tchen01/fadecandy/doc/images/controller-internals-diagram.png

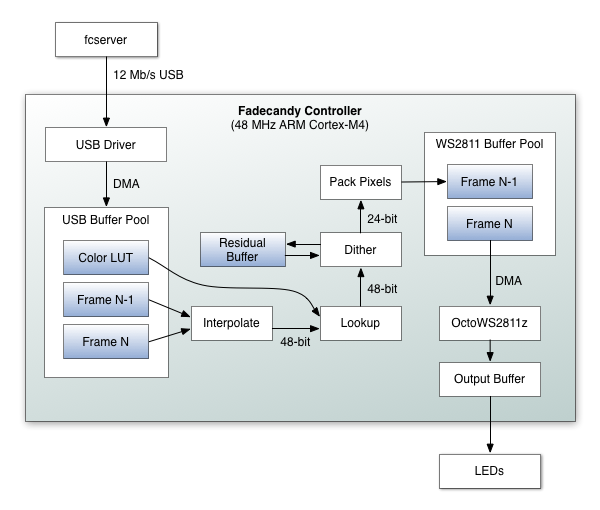
doc/images/controller-internals-diagram.png
