tchen01/fadecandy/doc/images/fc-title@2x.png

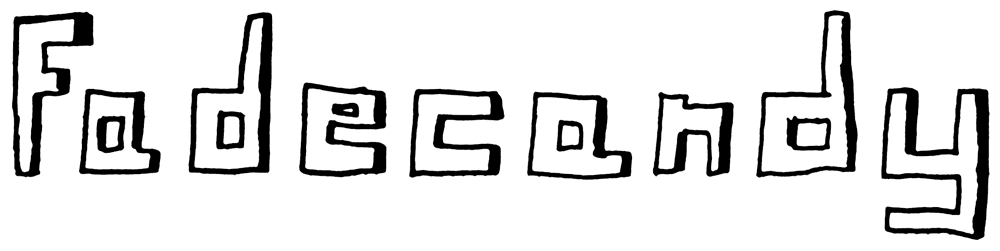
doc/images/fc-title@2x.png
