tchen01/fadecandy/doc/images/system-diagram-1.graffle/image2.png

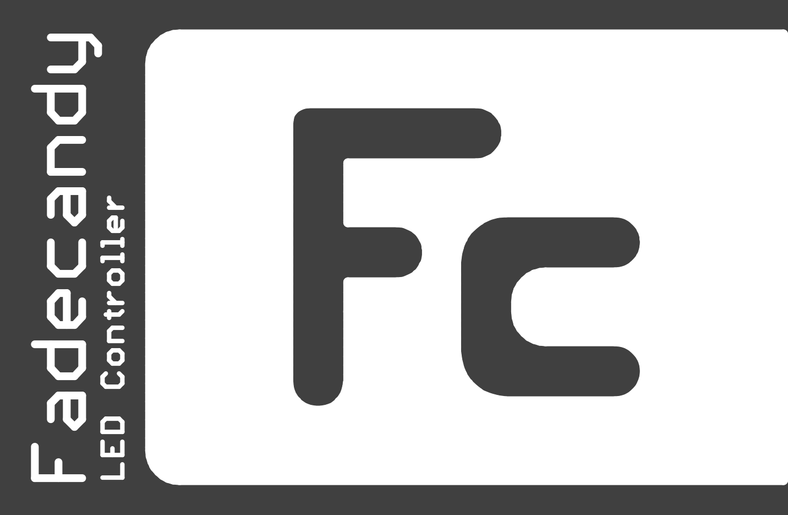
doc/images/system-diagram-1.graffle/image2.png
