tchen01/fadecandy/doc/images/system-diagram-2.png

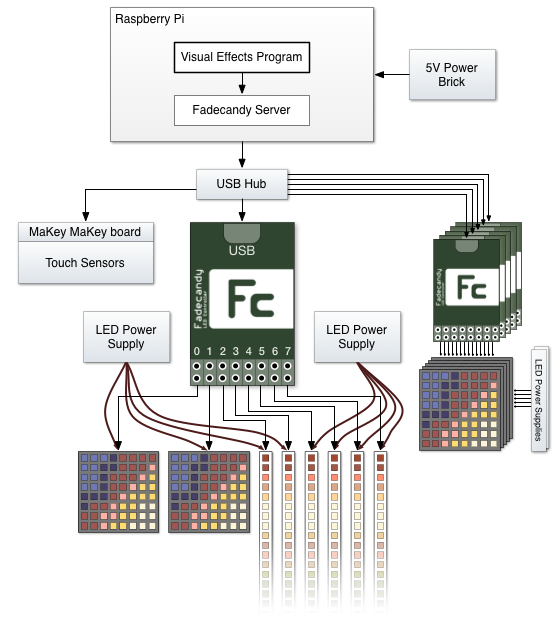
doc/images/system-diagram-2.png
