tchen01/fadecandy/examples/cpp/data/glass.png

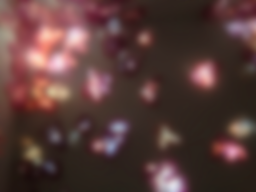
examples/cpp/data/glass.png
