tchen01/fadecandy/examples/cpp/data/sky.png

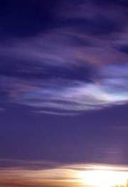
examples/cpp/data/sky.png
