tchen01/fadecandy/examples/p5js/images/flames.jpeg

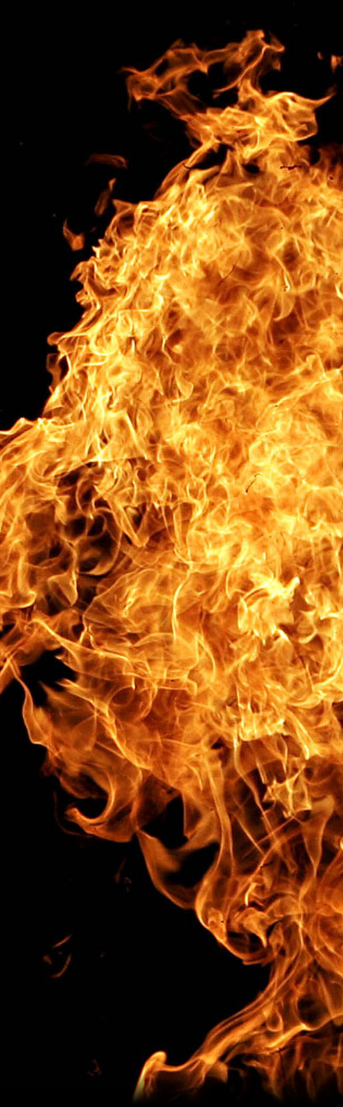
examples/p5js/images/flames.jpeg
