tchen01/fadecandy/examples/processing/grid24x8z_sequencer/data/checkers.png

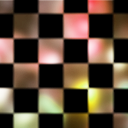
examples/processing/grid24x8z_sequencer/data/checkers.png
