tchen01/fadecandy/examples/processing/grid24x8z_sequencer/data/glass.jpeg

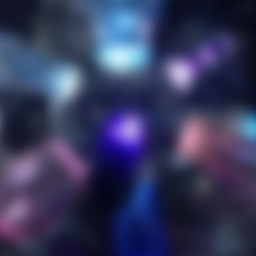
examples/processing/grid24x8z_sequencer/data/glass.jpeg
