tchen01/fadecandy/examples/processing/strip64_dot/data/color-dot.png

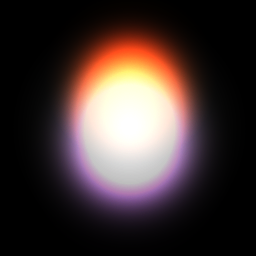
examples/processing/strip64_dot/data/color-dot.png
