tchen01/fadecandy/pcb/teensy3/wiring-diagram.png

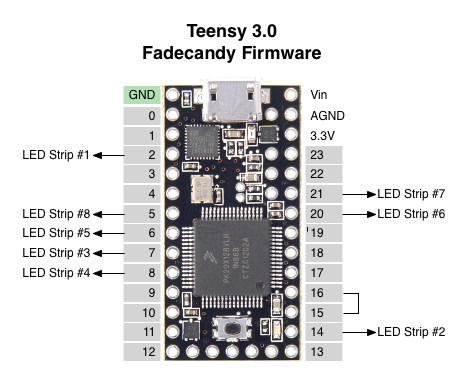
pcb/teensy3/wiring-diagram.png
