tchen01/fadecandy/firmware/fc_draw.cpp

/*
 * Fadecandy Firmware: Low-level draw buffer update code
 * (Included into fadecandy.cpp)
 * 
 * Copyright (c) 2013 Micah Elizabeth Scott
 * 
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
 * THE SOFTWARE IS PROVIDED "AS IS", WITHOUT WARRANTY OF ANY KIND, EXPRESS OR
 * IMPLIED, INCLUDING BUT NOT LIMITED TO THE WARRANTIES OF MERCHANTABILITY, FITNESS
 * FOR A PARTICULAR PURPOSE AND NONINFRINGEMENT. IN NO EVENT SHALL THE AUTHORS OR
 * COPYRIGHT HOLDERS BE LIABLE FOR ANY CLAIM, DAMAGES OR OTHER LIABILITY, WHETHER
 * IN AN ACTION OF CONTRACT, TORT OR OTHERWISE, ARISING FROM, OUT OF OR IN
 * CONNECTION WITH THE SOFTWARE OR THE USE OR OTHER DEALINGS IN THE SOFTWARE.
 */

static void FCP_FN(updateDrawBuffer)(unsigned interpCoefficient)
{
    /*
     * Update the LED draw buffer. In one step, we do the interpolation,
     * gamma correction, dithering, and we convert packed-pixel data to the
     * planar format used for OctoWS2811 DMAs.
     *
     * "interpCoefficient" indicates how far between fbPrev and fbNext
     * we are. It is a fixed point value in the range [0x0000, 0x10000],
     * corresponding to 100% fbPrev and 100% fbNext, respectively.
     */

    // For each pixel, this is a 24-byte stream of bits (6 words)
    uint32_t *out = (uint32_t*) leds.getDrawBuffer();

    /*
     * Interpolation coefficients, including a multiply by 257 to convert 8-bit color to 16-bit color.
     * You'd think that it would save clock cycles to calculate icPrev in updatePixel(), but this doesn't
     * seem to be the case.
     *
     * icPrev in range [0, 0x1010000]
     * icNext in range [0, 0x1010000]
     * icPrev + icNext = 0x1010000
     */

    uint32_t icPrev = 257 * (0x10000 - interpCoefficient);
    uint32_t icNext = 257 * interpCoefficient;

    /*
     * Pointer to the residual buffer for this pixel. Calculating this here rather than in updatePixel
     * saves a lot of clock cycles, since otherwise updatePixel() immediately needs to do a load from
     * constant pool and some multiplication.
     */

    residual_t *pResidual = residual;

    for (int i = 0; i < LEDS_PER_STRIP; ++i, pResidual += 3) {

        // Six output words
        union {
            uint32_t word;
            struct {
                uint32_t p0a:1, p1a:1, p2a:1, p3a:1, p4a:1, p5a:1, p6a:1, p7a:1,
                         p0b:1, p1b:1, p2b:1, p3b:1, p4b:1, p5b:1, p6b:1, p7b:1,
                         p0c:1, p1c:1, p2c:1, p3c:1, p4c:1, p5c:1, p6c:1, p7c:1,
                         p0d:1, p1d:1, p2d:1, p3d:1, p4d:1, p5d:1, p6d:1, p7d:1;
            };
        } o0, o1, o2, o3, o4, o5;

        /*
         * Remap bits.
         *
         * This generates compact and efficient code using the BFI instruction.
         */

        uint32_t p0 = FCP_FN(updatePixel)(icPrev, icNext,
            buffers.fbPrev->pixel(i + LEDS_PER_STRIP * 0),
            buffers.fbNext->pixel(i + LEDS_PER_STRIP * 0),
            pResidual + LEDS_PER_STRIP * 3 * 0);

        o5.p0d = p0;
        o5.p0c = p0 >> 1;
        o5.p0b = p0 >> 2;
        o5.p0a = p0 >> 3;
        o4.p0d = p0 >> 4;
        o4.p0c = p0 >> 5;
        o4.p0b = p0 >> 6;
        o4.p0a = p0 >> 7;
        o3.p0d = p0 >> 8;
        o3.p0c = p0 >> 9;
        o3.p0b = p0 >> 10;
        o3.p0a = p0 >> 11;
        o2.p0d = p0 >> 12;
        o2.p0c = p0 >> 13;
        o2.p0b = p0 >> 14;
        o2.p0a = p0 >> 15;
        o1.p0d = p0 >> 16;
        o1.p0c = p0 >> 17;
        o1.p0b = p0 >> 18;
        o1.p0a = p0 >> 19;
        o0.p0d = p0 >> 20;
        o0.p0c = p0 >> 21;
        o0.p0b = p0 >> 22;
        o0.p0a = p0 >> 23;

        uint32_t p1 = FCP_FN(updatePixel)(icPrev, icNext,
            buffers.fbPrev->pixel(i + LEDS_PER_STRIP * 1),
            buffers.fbNext->pixel(i + LEDS_PER_STRIP * 1),
            pResidual + LEDS_PER_STRIP * 3 * 1);

        o5.p1d = p1;
        o5.p1c = p1 >> 1;
        o5.p1b = p1 >> 2;
        o5.p1a = p1 >> 3;
        o4.p1d = p1 >> 4;
        o4.p1c = p1 >> 5;
        o4.p1b = p1 >> 6;
        o4.p1a = p1 >> 7;
        o3.p1d = p1 >> 8;
        o3.p1c = p1 >> 9;
        o3.p1b = p1 >> 10;
        o3.p1a = p1 >> 11;
        o2.p1d = p1 >> 12;
        o2.p1c = p1 >> 13;
        o2.p1b = p1 >> 14;
        o2.p1a = p1 >> 15;
        o1.p1d = p1 >> 16;
        o1.p1c = p1 >> 17;
        o1.p1b = p1 >> 18;
        o1.p1a = p1 >> 19;
        o0.p1d = p1 >> 20;
        o0.p1c = p1 >> 21;
        o0.p1b = p1 >> 22;
        o0.p1a = p1 >> 23;

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
        o0.p7d = p7 >> 20;
        o0.p7c = p7 >> 21;
        o0.p7b = p7 >> 22;
        o0.p7a = p7 >> 23;

        *(out++) = o0.word;
        *(out++) = o1.word;
        *(out++) = o2.word;
        *(out++) = o3.word;
        *(out++) = o4.word;
        *(out++) = o5.word;
    }
}
