tchen01/fadecandy/firmware/wiring.h

/*
  wiring.h - Partial implementation of the Wiring API for the ATmega8.
  Part of Arduino - http://www.arduino.cc/

  Copyright (c) 2005-2006 David A. Mellis

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
  $Id: wiring.h 387 2008-03-08 21:30:00Z mellis $
*/

#ifndef Wiring_h
#define Wiring_h

#include <stdint.h>
#include <stdlib.h>
#include "core_pins.h"

#ifdef __cplusplus
extern "C"{
#endif

#define true 1
#define false 0

#define PI 3.1415926535897932384626433832795
#define HALF_PI 1.5707963267948966192313216916398
#define TWO_PI 6.283185307179586476925286766559
#define DEG_TO_RAD 0.017453292519943295769236907684886
#define RAD_TO_DEG 57.295779513082320876798154814105

#ifndef M_PI
#define M_PI 3.1415926535897932384626433832795
#endif
#ifndef M_SQRT2
#define M_SQRT2 1.4142135623730950488016887
#endif

#define SERIAL  0
#define DISPLAY 1

// undefine stdlib's abs if encountered
#ifdef abs
#undef abs
#endif

#define min(a,b) ((a)<(b)?(a):(b))
#define max(a,b) ((a)>(b)?(a):(b))
#define abs(x) ((x)>0?(x):-(x))
#define constrain(amt,low,high) ((amt)<(low)?(low):((amt)>(high)?(high):(amt)))
#define round(x)     ((x)>=0?(long)((x)+0.5):(long)((x)-0.5))
#define radians(deg) ((deg)*DEG_TO_RAD)
#define degrees(rad) ((rad)*RAD_TO_DEG)
#define sq(x) ((x)*(x))

#define sei() __enable_irq()
#define cli() __disable_irq()
#define interrupts() __enable_irq()
#define noInterrupts() __disable_irq()

#define clockCyclesPerMicrosecond() ( F_CPU / 1000000L )
#define clockCyclesToMicroseconds(a) ( (a) / clockCyclesPerMicrosecond() )
#define microsecondsToClockCycles(a) ( (a) * clockCyclesPerMicrosecond() )

#define lowByte(w) ((uint8_t)((w) & 0xFF))
#define highByte(w) ((uint8_t)((w) >> 8))

#define bitRead(value, bit) (((value) >> (bit)) & 0x01)
#define bitSet(value, bit) ((value) |= (1UL << (bit)))
#define bitClear(value, bit) ((value) &= ~(1UL << (bit)))
#define bitWrite(value, bit, bitvalue) (bitvalue ? bitSet(value, bit) : bitClear(value, bit))

typedef unsigned int word;

#define bit(b) (1UL << (b))

typedef uint8_t boolean;
typedef uint8_t byte;

uint32_t pulseIn(uint8_t pin, uint8_t state, uint32_t timeout);
void shiftOut(uint8_t dataPin, uint8_t clockPin, uint8_t bitOrder, byte val);

void setup(void);
void loop(void);

#ifdef __cplusplus
} // extern "C"
#endif

#endif
