tchen01/fadecandy/examples/processing/template/template.pde

// This is an empty Processing sketch with support for Fadecandy.

OPC opc;

void setup()
{
  size(600, 300);
  opc = new OPC(this, "127.0.0.1", 7890);

  // Set up your LED mapping here
}

void draw()
{
  background(0);

  // Draw each frame here
}
