tchen01/fadecandy/examples/cpp/particle_trail.cpp

#include "lib/effect_runner.h"
#include "particle_trail.h"

int main(int argc, char **argv)
{
    EffectRunner r;
    ParticleTrailEffect e;
    r.setEffect(&e);
    r.setLayout("../layouts/grid32x16z.json");
    return r.main(argc, argv);
}
